SolidHal/noisedeck/demos/early_assembly/full_open.gif

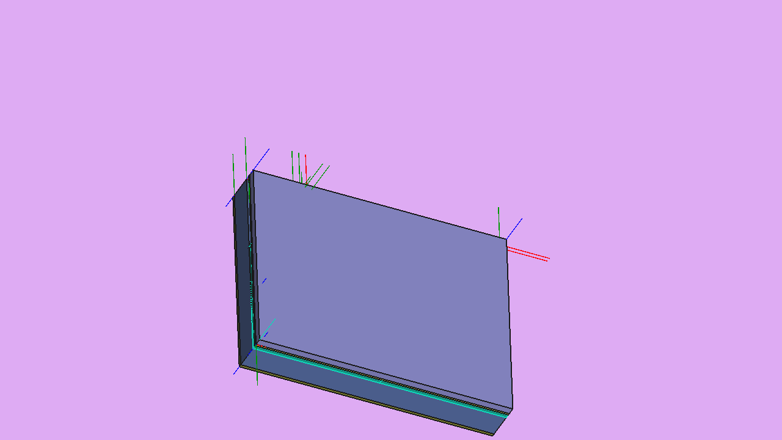
demos/early_assembly/full_open.gif
